jglandorf/VLDO/design/vldo_nd6t1.asc

C1: cap; 1µ; V=20
C2: cap; 0.1; V=20
C3: cap; 0.1µ; V=20
M1: pmos; irf4905
Q1: npn; 2N2222
Q2: npn; 2N2222
R1: res; 100k; tol=1 pwr=0.125
R2: res; 10k; tol=1 pwr=0.125
R3: res; 30k; tol=1 pwr=0.125
R4: res; 22k; tol=1 pwr=0.125
R5: res; 6; tol=1 pwr=50
R6: res; 0.05; tol=1 pwr=100
U2: LT1121-5
V1: voltage; 12; Rser=0.05
Named nets: 0, Vout, Vin, Vldo, Vs
.SUBCKT irf4905 1 2 3
**************************************
*      Model Generated by MODPEX     *
*Copyright(c) Symmetry Design Systems*
*         All Rights Reserved        *
*    UNPUBLISHED LICENSED SOFTWARE   *
*   Contains Proprietary Information *
*      Which is The Property of      *
*     SYMMETRY OR ITS LICENSORS      *
*Commercial Use or Resale Restricted *
*   by Symmetry License Agreement    *
**************************************
* Model generated on Jun 19, 96
* Model format: SPICE3
* Symmetry POWER MOS Model (Version 1.0)
* External Node Designations
* Node 1 -> Drain
* Node 2 -> Gate
* Node 3 -> Source
M1 9 7 8 8 MM L=100u W=100u
* Default values used in MM:
* The voltage-dependent capacitances are
* not included. Other default values are:
*   RS=0 RD=0 LD=0 CBD=0 CBS=0 CGBO=0
.MODEL MM PMOS LEVEL=1 IS=1e-32
+VTO=-3.53713 LAMBDA=0.00549383 KP=23.3701
+CGSO=2.84439e-05 CGDO=1e-11
RS 8 3 0.0101265
D1 1 3 MD
.MODEL MD D IS=1.29014e-08 RS=0.00297795 N=1.46717 BV=55
+IBV=0.00025 EG=1.2 XTI=4 TT=0
+CJO=3.56968e-09 VJ=1.17553 M=0.500933 FC=0.5
RDS 3 1 2.2e+06
RD 9 1 0.0001
RG 2 7 6
D2 5 4 MD1
* Default values used in MD1:
*   RS=0 EG=1.11 XTI=3.0 TT=0
*   BV=infinite IBV=1mA
.MODEL MD1 D IS=1e-32 N=50
+CJO=4.83772e-09 VJ=0.625334 M=0.543532 FC=1e-08
D3 5 0 MD2
* Default values used in MD2:
*   EG=1.11 XTI=3.0 TT=0 CJO=0
*   BV=infinite IBV=1mA
.MODEL MD2 D IS=1e-10 N=0.4 RS=3e-06
RL 5 10 1
FI2 7 9 VFI2 -1
VFI2 4 0 0
EV16 10 0 9 7 1
CAP 11 10 6.08035e-09
FI1 7 9 VFI1 -1
VFI1 11 6 0
RCAP 6 10 1
D4 6 0 MD3
* Default values used in MD3:
*   EG=1.11 XTI=3.0 TT=0 CJO=0
*   RS=0 BV=infinite IBV=1mA
.MODEL MD3 D IS=1e-10 N=0.4
.ENDS
.tran 0 0.5 0
Vldo = Vout * (R4 / (R3 + R4))
Vout = Vldo / (R4 / (R3 + R4))
11.8V = 5V / ( 22k / (30k + 22k))
8.85V = 5V / (39k / (30k + 39k))
References:
https://www.gqrp.com/limiter.jpg
http://www.nd6t.com/qrp/VLDO.htm
